spezifisch/esphome-entry/docs/schematics/esphome-entry board/esphome-entry board.kicad_sch

## KiCad design docs/schematics/esphome-entry board/esphome-entry board.kicad_sch (2024-09-17)

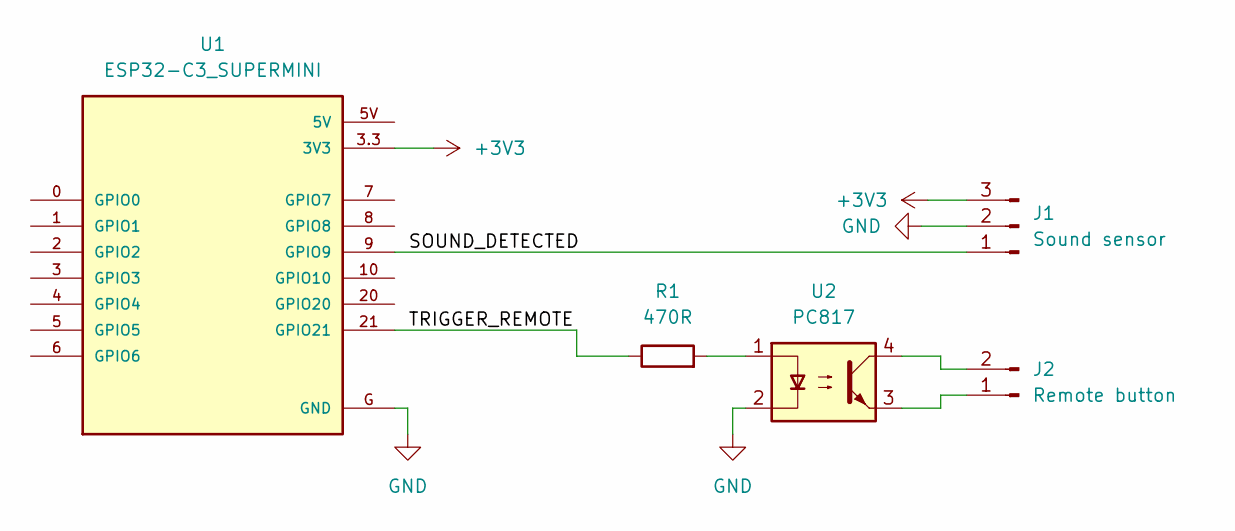
[picture p4: schematic esphome-entry board.kicad_sch]

Parts:
J1: Sound sensor
J2: Remote button
R1: 470R
U1: ESP32-C3_SUPERMINI; MODULE_ESP32-C3_SUPERMINI
U2: PC817; DIP-4_W7.62mm

Connections:
+3V3: J1.3, U1.3.3 (3V3)
GND: J1.2, U1.G (GND), U2.2
unnamed: J2.1, U2.3
unnamed: J2.2, U2.4
unnamed: R1.2, U2.1
SOUND_DETECTED: J1.1, U1.9 (GPIO9)
TRIGGER_REMOTE: R1.1, U1.21 (GPIO21)
