spezifisch/esphome-entry/docs/schematics/sound trigger sensor/sound trigger sensor.kicad_sch

## KiCad design docs/schematics/sound trigger sensor/sound trigger sensor.kicad_sch (2024-09-17, an earlier design)

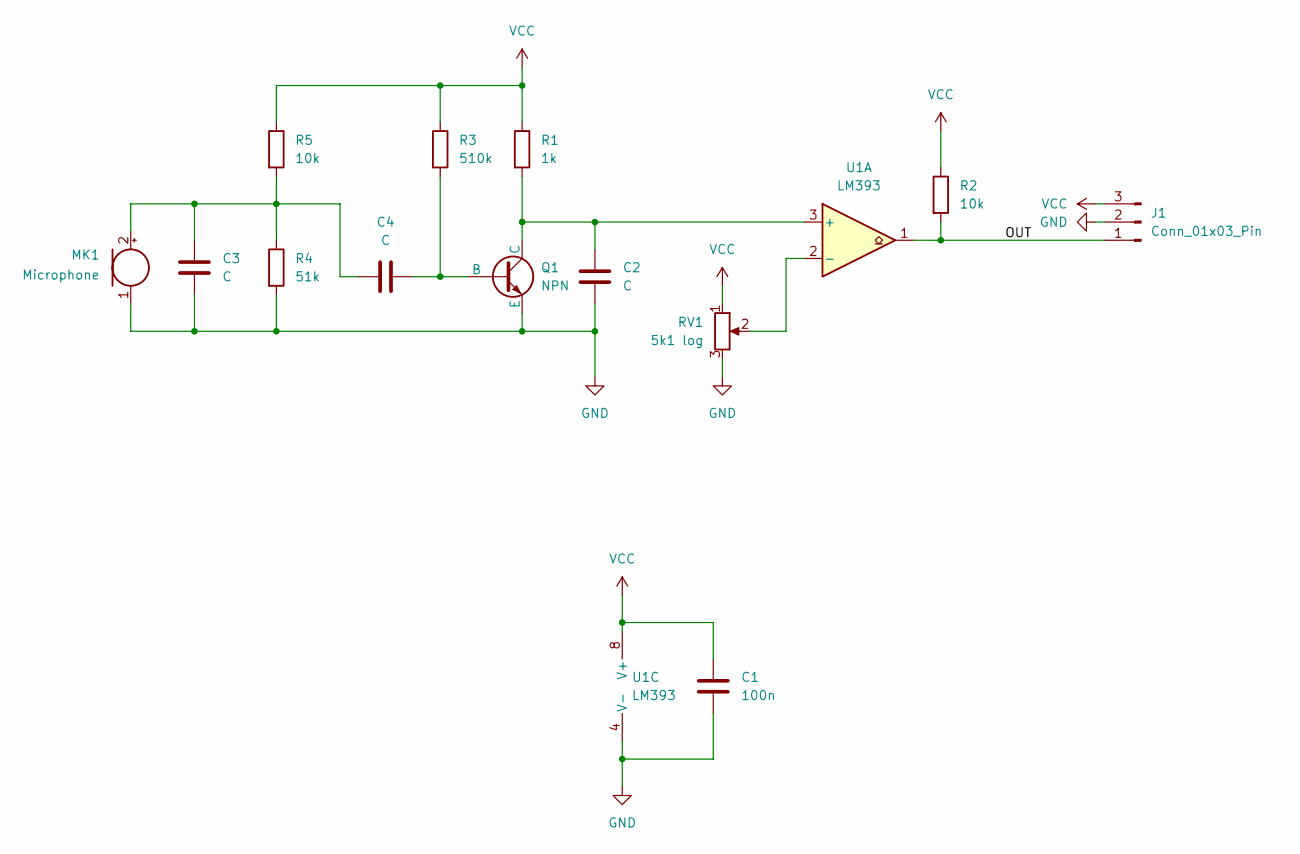
[picture p5: schematic sound trigger sensor.kicad_sch]

Parts:
C1: 100n
C2, C3, C4: C
J1: Conn_01x03_Pin
MK1: Microphone
Q1: NPN
R1: 1k
R2, R5: 10k
R3: 510k
R4: 51k
RV1: 5k1 log
U1: LM393

Connections:
GND: C1.2, C2.2, C3.2, J1.2, MK1.1 (-), Q1.3 (E), R4.2, RV1.3, U1.4 (V-)
unnamed: C2.1, Q1.1 (C), R1.2, U1.3 (+)
unnamed: C3.1, C4.1, MK1.2 (+), R4.1, R5.2
unnamed: C4.2, Q1.2 (B), R3.2
unnamed: RV1.2, U1.2 (-)
OUT: J1.1, R2.2, U1.1
VCC: C1.1, J1.3, R1.1, R2.1, R3.1, R5.1, RV1.1, U1.8 (V+)
